sparkfun/OpenScale/Documentation/2016-08-01.png

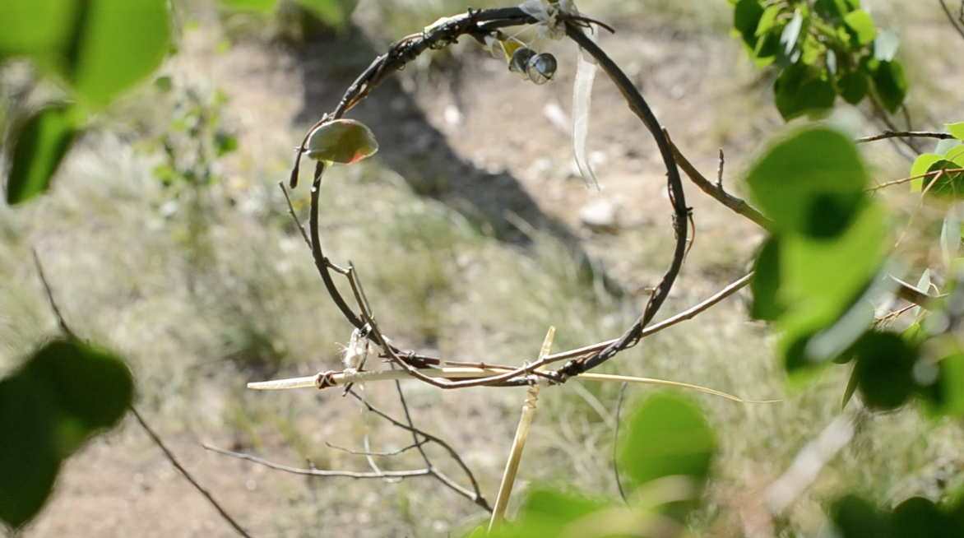
Documentation/2016-08-01.png
