sparkfun/OpenScale/Documentation/5702ccd4-451b-4da7-a7df-f7d7936824c6.jpg

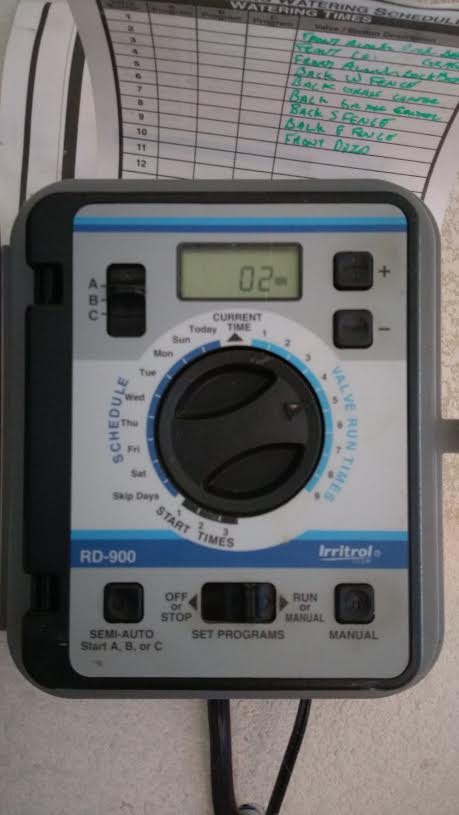
Documentation/5702ccd4-451b-4da7-a7df-f7d7936824c6.jpg
