sparkfun/OpenScale/Documentation/13261-04.jpg

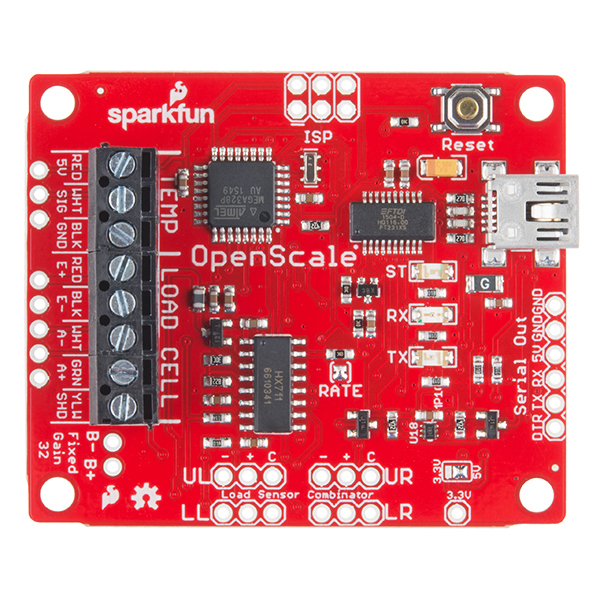
Documentation/13261-04.jpg
