sparkfun/OpenScale/Documentation/dataSparkfun.PNG

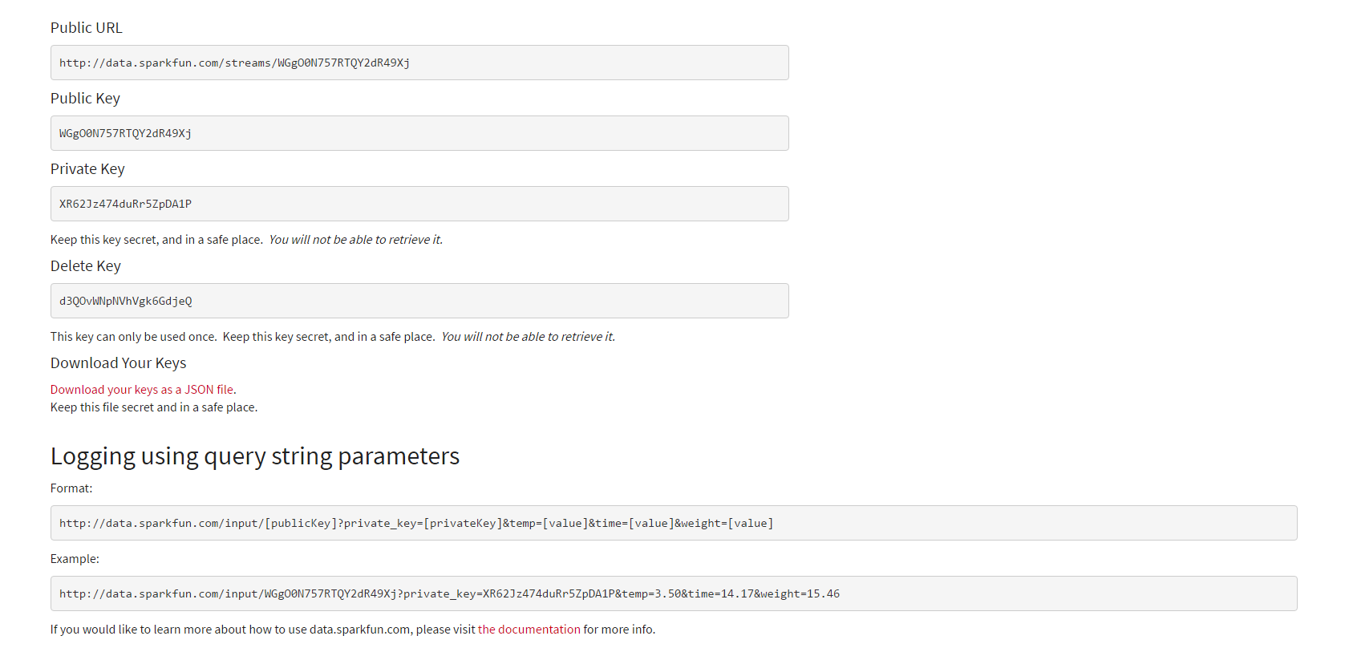
Documentation/dataSparkfun.PNG
