sparkfun/OpenScale/Documentation/e4b5a238-1e85-4022-83e2-9f93669ab543.jpg

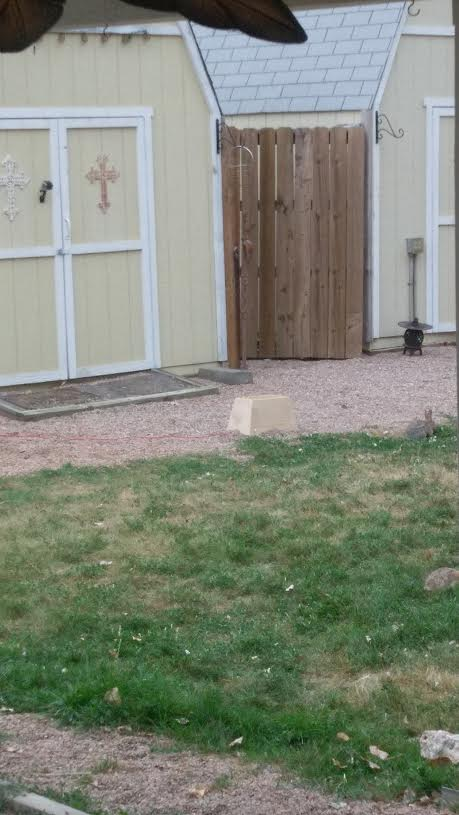
Documentation/e4b5a238-1e85-4022-83e2-9f93669ab543.jpg
