sparkfun/OpenScale/Documentation/Fuse_Settings.PNG

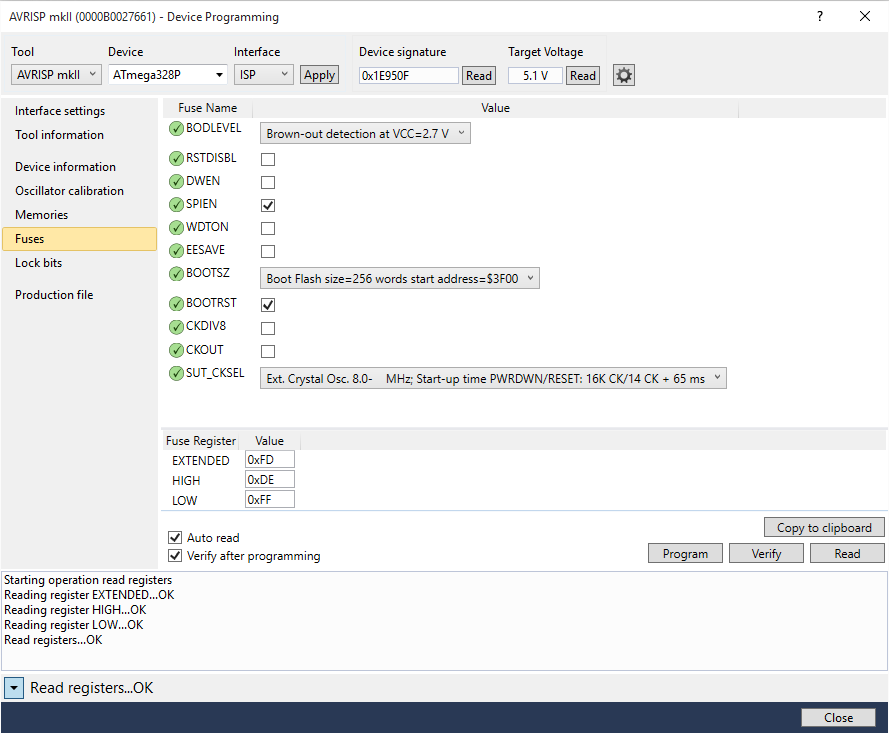
Documentation/Fuse_Settings.PNG
