sparkfun/OpenScale/Documentation/getoffmylawn.png

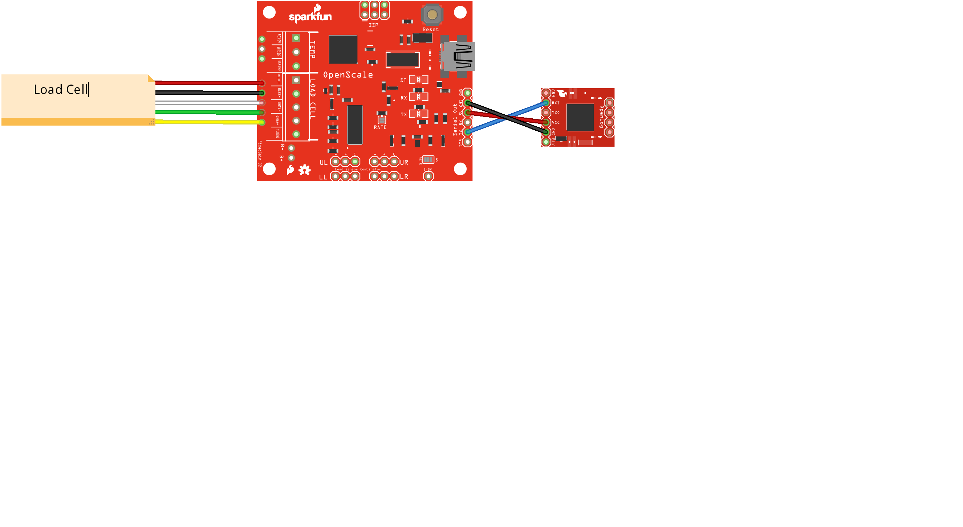
Documentation/getoffmylawn.png
