sparkfun/OpenScale/Documentation/Outdoor setup.jpg

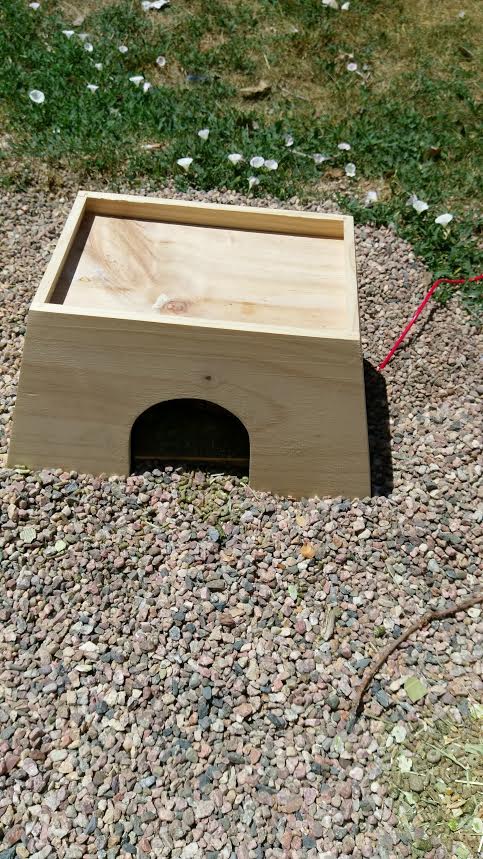
Documentation/Outdoor setup.jpg
