sparkfun/OpenScale/Documentation/Calibration2.PNG

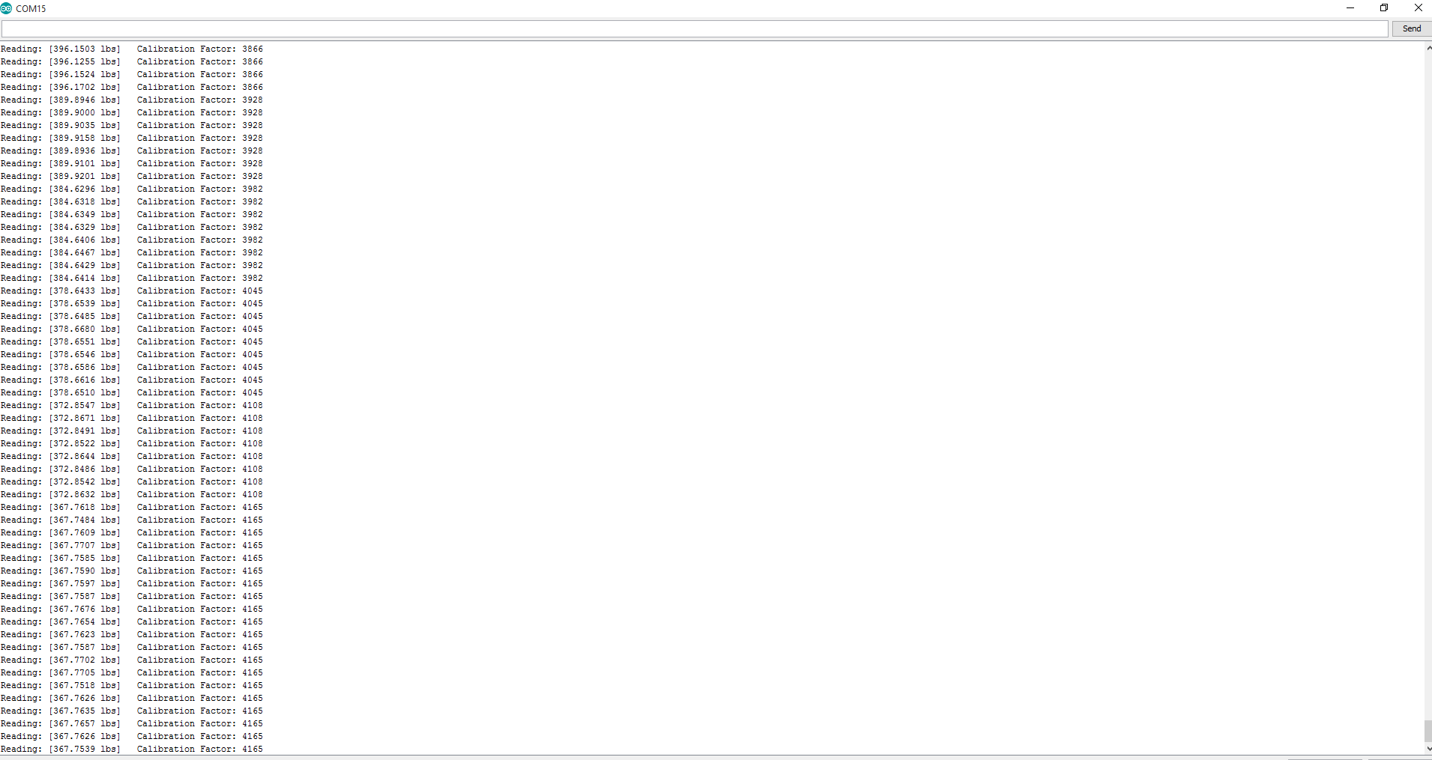
Documentation/Calibration2.PNG
